Hal9k-dk/kamstrup/pcb/kamstrup-pcb.png

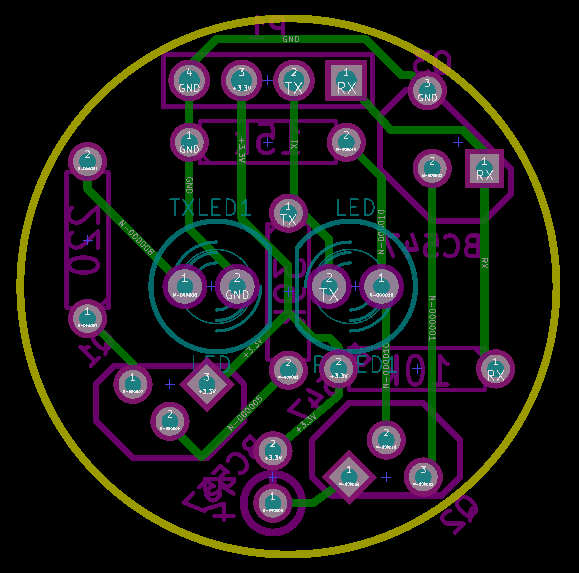
pcb/kamstrup-pcb.png
