Hal9k-dk/kamstrup/pics/IMG_20160121_083032.jpg

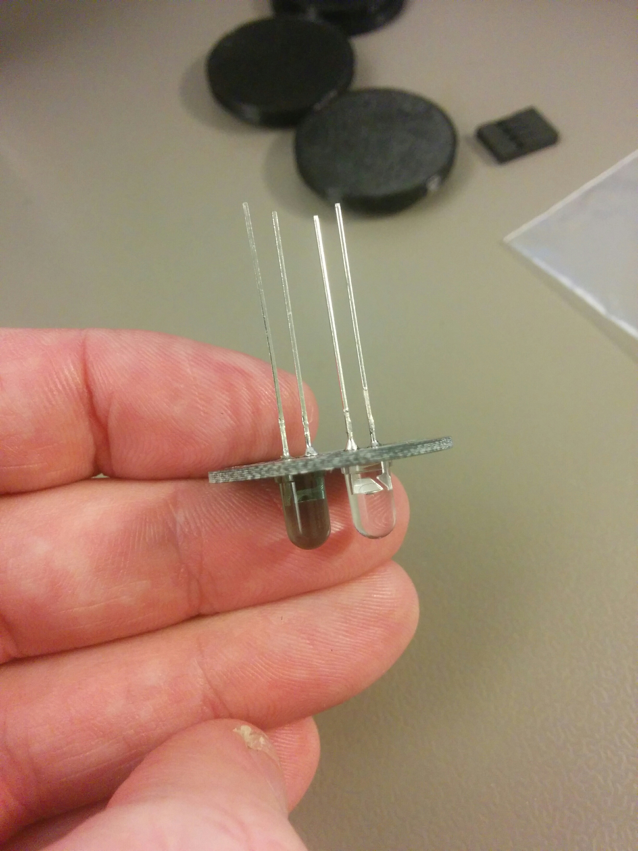
pics/IMG_20160121_083032.jpg
