Hal9k-dk/kamstrup/pics/IMG_20160121_084500.jpg

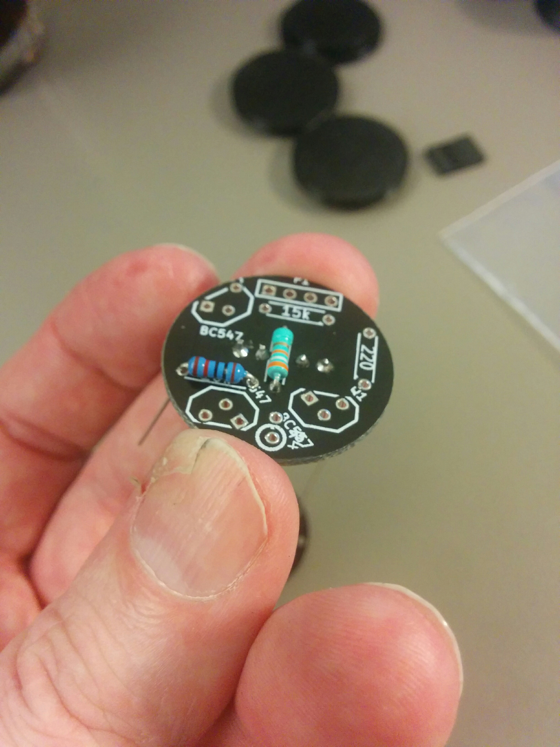
pics/IMG_20160121_084500.jpg
