Hal9k-dk/kamstrup/pics/IMG_20160121_085957.jpg

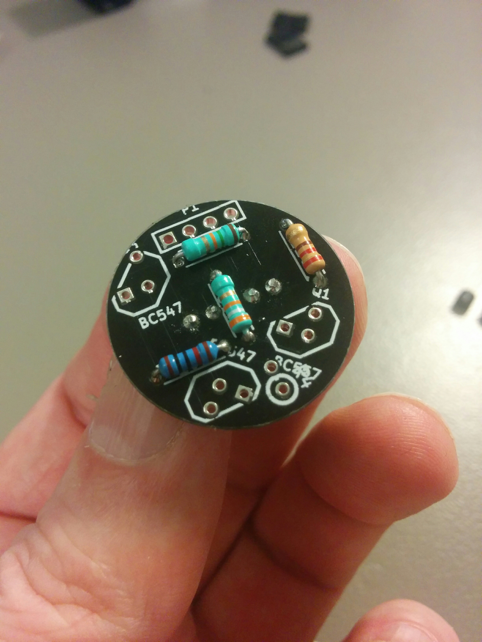
pics/IMG_20160121_085957.jpg
