Hal9k-dk/kamstrup/pics/IMG_20160121_090242.jpg

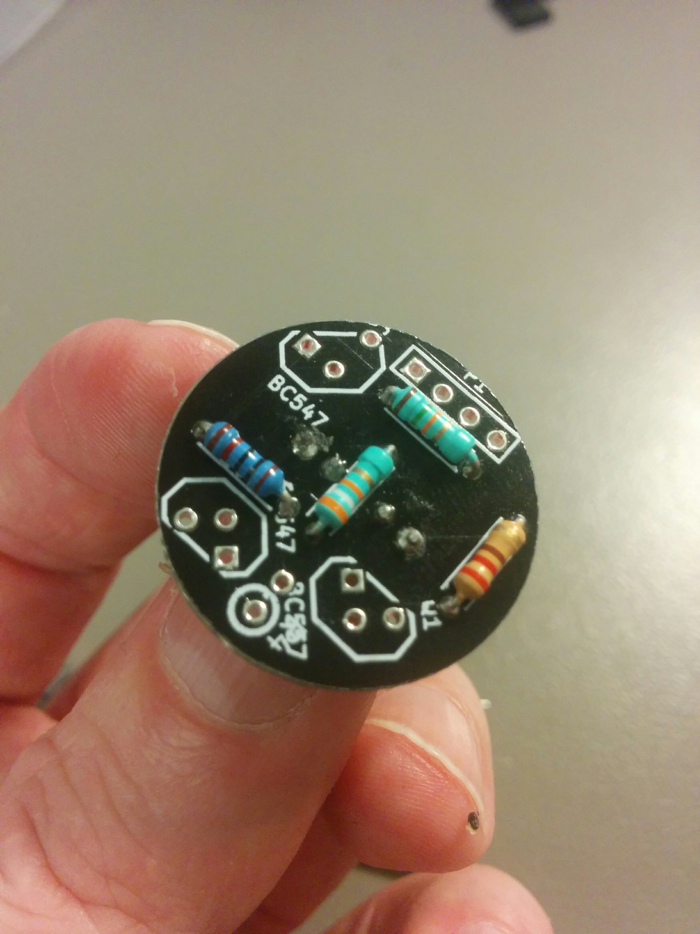
pics/IMG_20160121_090242.jpg
