Hal9k-dk/kamstrup/pics/IMG_20160121_091058.jpg

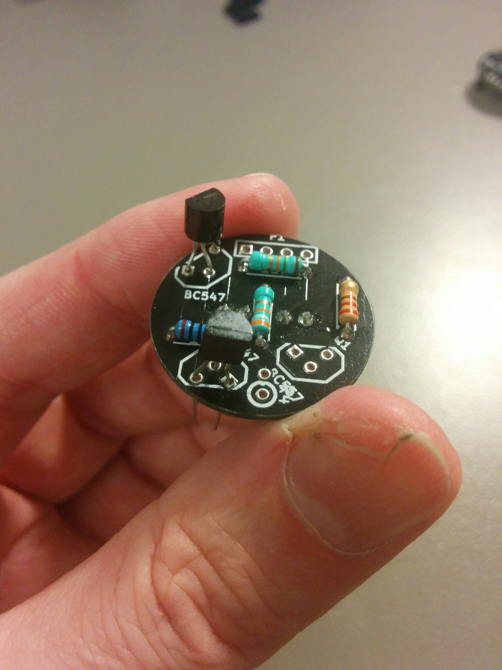
pics/IMG_20160121_091058.jpg
