Hal9k-dk/kamstrup/pics/IMG_20160121_092514.jpg

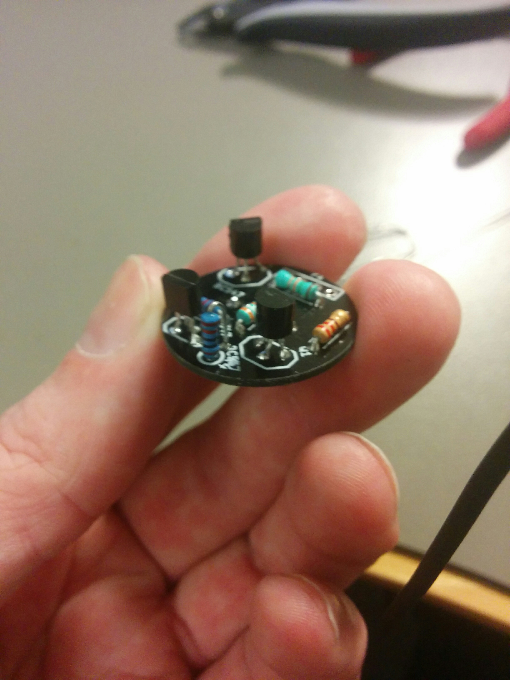
pics/IMG_20160121_092514.jpg
