Hal9k-dk/kamstrup/pics/IMG_20160121_092517.jpg

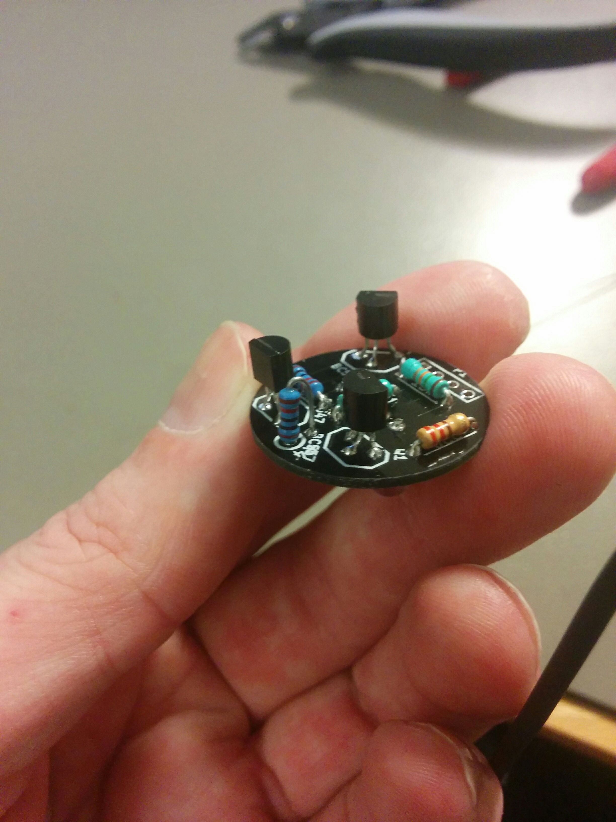
pics/IMG_20160121_092517.jpg
