Hal9k-dk/kamstrup/pics/IMG_20160121_093010.jpg

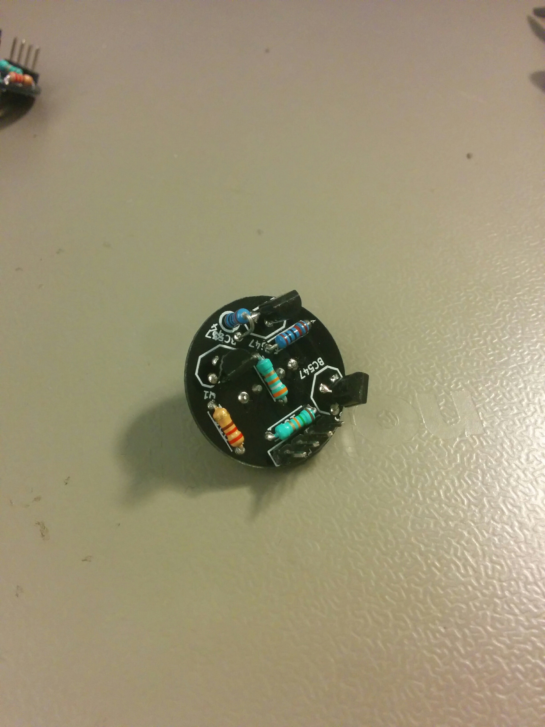
pics/IMG_20160121_093010.jpg
