Hal9k-dk/kamstrup/pics/IMG_20160121_093027.jpg

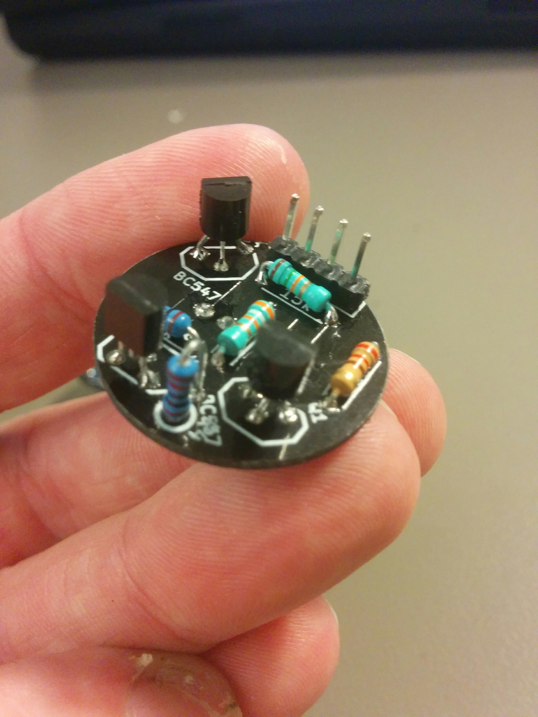
pics/IMG_20160121_093027.jpg
