Hal9k-dk/kamstrup/pics/IMG_20160121_093034.jpg

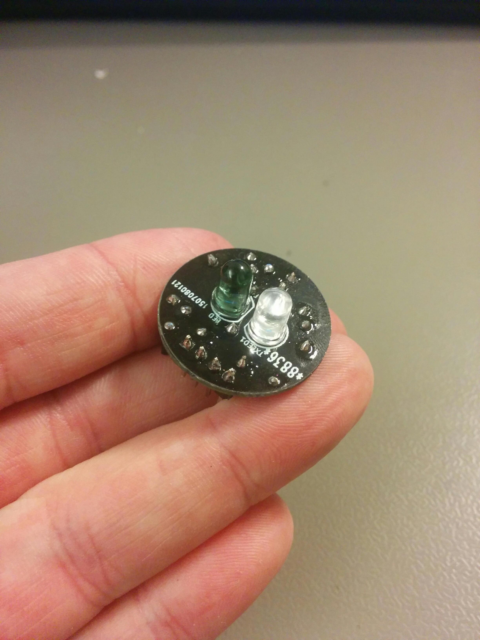
pics/IMG_20160121_093034.jpg
