Hal9k-dk/kamstrup/pics/kamstrup39k.jpg

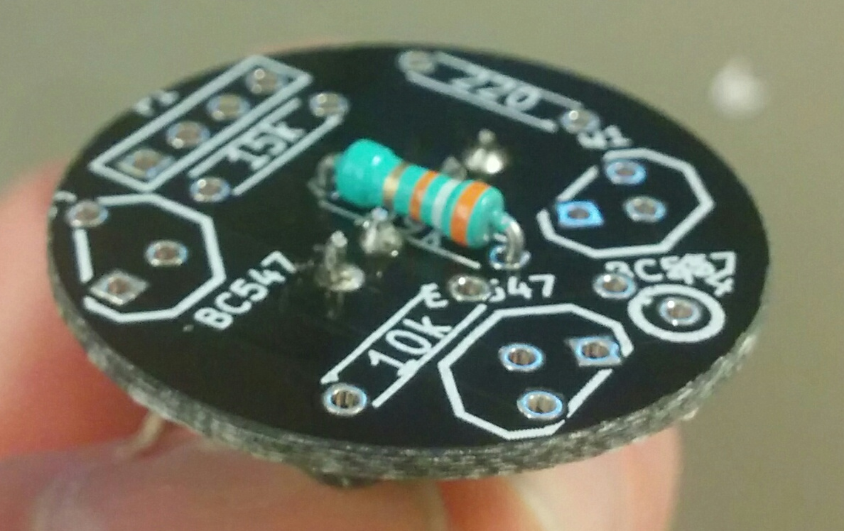
pics/kamstrup39k.jpg
