Hal9k-dk/kamstrup/pics/kamstrupbc547.jpg

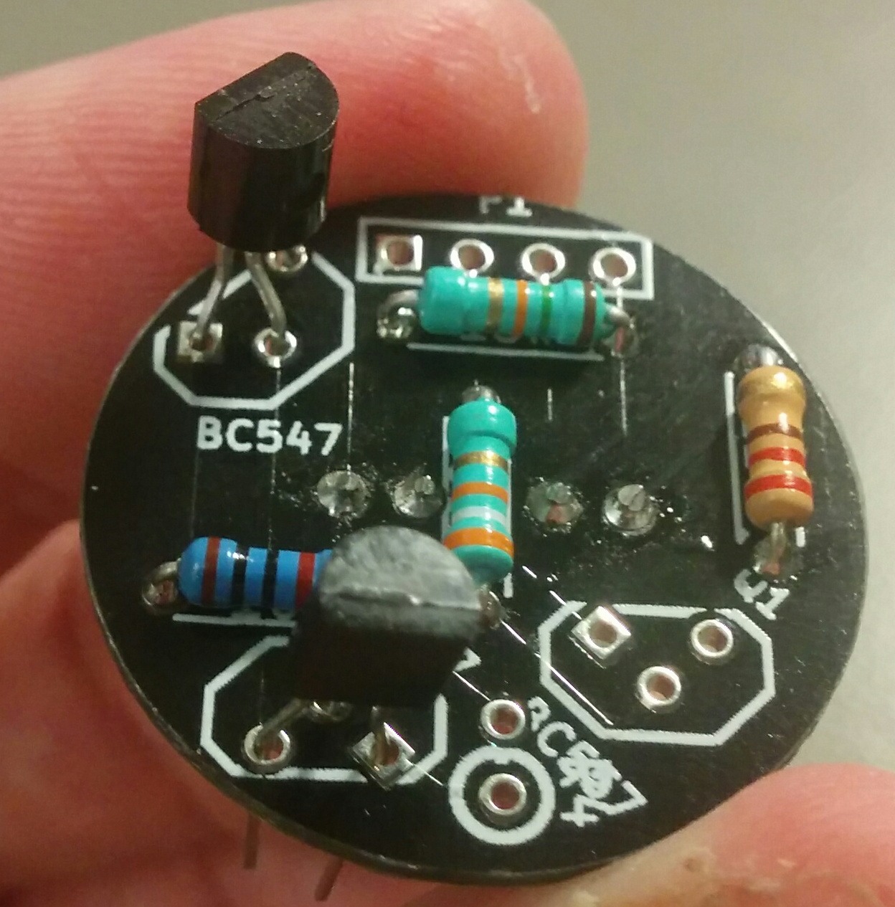
pics/kamstrupbc547.jpg
