Hal9k-dk/kamstrup/pics/kamstrupbc557.jpg

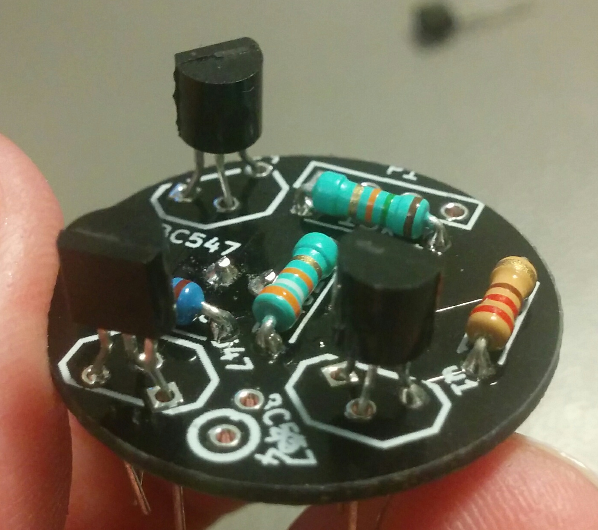
pics/kamstrupbc557.jpg
