Hal9k-dk/kamstrup/pics/kamstrupkit.jpg

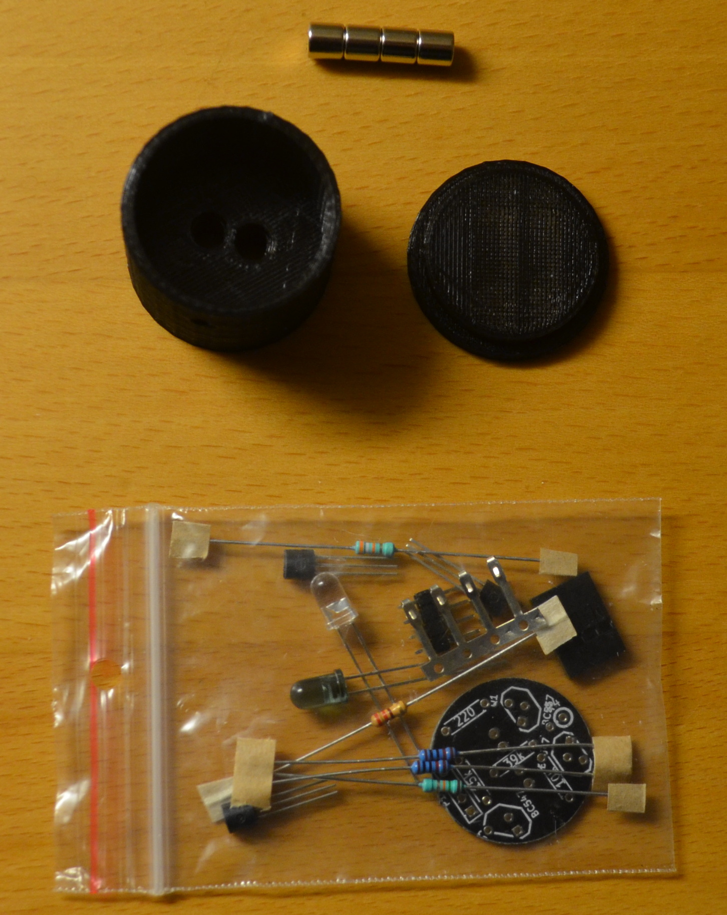
pics/kamstrupkit.jpg
