Hal9k-dk/kamstrup/pics/kamstrupmodstande.jpg

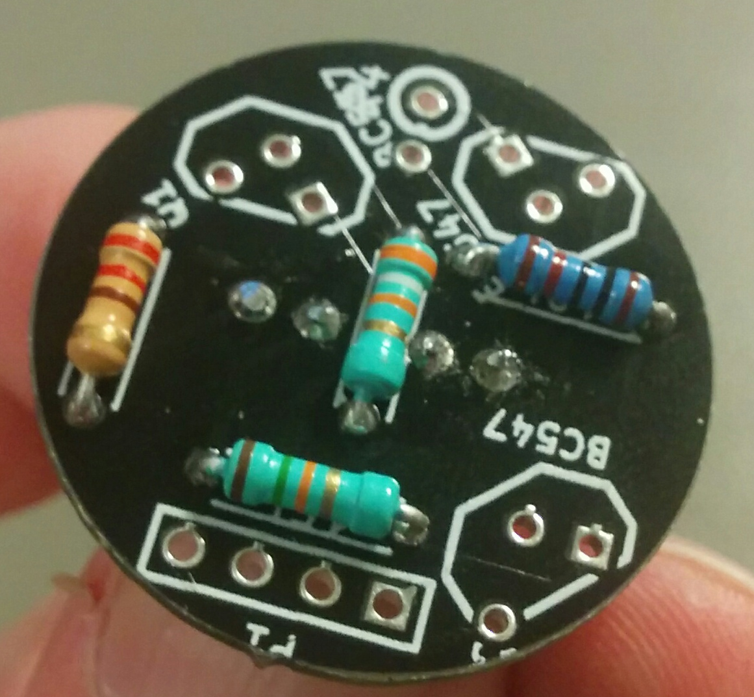
pics/kamstrupmodstande.jpg
